c0pperdragon/Atari2600Module/EPROMer/adventure_pal.h

76,239,242,120,216,76,6,243,133,43,165,134,162,0,32,210,
240,165,136,162,1,32,210,240,165,139,162,4,32,210,240,133,
2,133,42,133,44,165,140,56,233,4,133,141,173,132,2,208,
251,169,0,133,144,133,145,133,143,133,28,169,1,133,38,169,
104,133,142,164,143,177,128,133,13,200,177,128,133,14,200,177,
128,133,15,200,132,143,133,2,169,0,133,1,76,114,240,165,
142,56,229,137,133,2,16,10,164,145,177,132,133,28,240,2,
230,145,162,0,165,142,56,229,135,16,9,164,144,177,130,170,
240,2,230,144,160,0,165,142,56,229,141,41,252,208,2,160,
2,165,142,41,15,208,38,133,2,132,31,134,27,164,143,177,
128,133,13,200,177,128,133,14,200,177,128,133,15,200,132,143,
198,142,165,142,201,8,16,167,133,1,76,198,240,133,2,132,
31,134,27,76,176,240,169,0,133,28,133,27,169,61,141,150,
2,96,160,2,56,200,233,15,176,251,73,255,233,6,10,10,
10,10,132,2,136,16,253,149,16,149,32,96,173,132,2,208,
251,169,2,133,2,133,1,133,2,133,2,133,2,133,0,133,
2,133,2,169,0,133,2,133,0,169,72,141,150,2,96,165,
138,32,113,242,160,0,177,147,133,128,160,1,177,147,133,129,
173,130,2,41,8,240,12,160,2,177,147,32,211,242,133,8,
76,60,241,160,3,177,147,32,211,242,133,8,169,8,32,211,
242,133,9,160,4,177,147,133,10,41,192,74,74,74,74,74,
133,30,74,133,29,32,53,242,165,149,201,0,240,10,201,90,
208,18,165,150,201,0,240,12,165,149,133,216,165,150,133,149,
165,216,133,150,166,149,189,68,255,133,147,189,69,255,133,148,
160,1,177,147,133,134,160,2,177,147,133,135,189,70,255,133,
147,189,71,255,133,148,160,0,177,147,133,220,189,72,255,133,
147,189,73,255,133,148,32,161,242,200,177,147,133,130,200,177,
147,133,131,173,130,2,41,8,240,11,189,74,255,32,211,242,
133,6,76,205,241,189,75,255,32,211,242,133,6,189,76,255,
9,16,133,4,166,150,189,68,255,133,147,189,69,255,133,148,
160,1,177,147,133,136,160,2,177,147,133,137,189,70,255,133,
147,189,71,255,133,148,160,0,177,147,133,220,189,72,255,133,
147,189,73,255,133,148,32,161,242,200,177,147,133,132,200,177,
147,133,133,173,130,2,41,8,240,11,189,74,255,32,211,242,
133,7,76,45,242,189,75,255,32,211,242,133,7,189,76,255,
9,16,133,5,96,164,156,169,162,133,149,133,150,152,24,105,
9,201,162,144,2,169,0,168,185,68,255,133,147,185,69,255,
133,148,162,0,161,147,197,138,208,16,165,149,201,162,208,5,
132,149,76,106,242,132,150,76,110,242,196,156,208,207,132,156,
96,133,216,133,147,169,0,133,148,24,38,147,38,148,38,147,
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
