c0pperdragon/Atari2600Module/EPROMer/atlantis_pal.h

120,216,162,255,154,232,138,149,0,232,208,251,134,211,169,1,
133,142,133,197,133,198,133,239,32,175,28,169,2,133,1,133,
2,133,0,133,2,133,2,133,2,169,0,133,0,169,75,141,
150,2,173,130,2,102,142,176,4,74,176,47,42,74,38,142,
74,36,140,144,4,38,140,208,90,16,21,165,250,41,31,133,
140,230,141,165,141,201,4,208,15,169,0,133,141,76,104,16,
165,140,69,250,41,31,240,227,76,117,16,169,1,133,142,133,
211,133,249,208,6,169,0,133,249,133,211,169,10,133,244,133,
240,169,1,133,247,32,175,28,169,0,133,239,133,238,133,236,
133,246,133,245,133,161,133,162,133,163,133,219,162,6,149,212,
202,16,251,165,211,48,4,208,44,240,26,198,242,208,22,198,
243,208,18,32,175,28,169,0,133,238,133,211,133,245,162,6,
149,212,202,16,251,162,0,134,236,134,190,134,196,165,224,208,
4,165,12,16,150,162,10,169,31,149,129,169,100,149,128,202,
202,16,244,165,239,240,15,162,10,169,110,149,128,24,105,10,
202,202,16,247,48,73,165,249,208,12,165,141,24,105,1,32,
232,30,133,128,208,57,162,0,134,158,162,2,160,8,181,161,
74,74,74,74,32,232,30,208,4,165,158,240,7,230,158,165,
143,153,130,0,181,161,41,15,32,232,30,208,4,165,158,240,
7,230,158,165,143,153,128,0,202,136,136,136,136,16,207,162,
6,134,241,181,212,240,54,201,5,240,10,165,250,41,7,208,
16,246,212,16,12,198,241,16,8,165,248,208,4,169,255,133,
211,180,212,136,224,6,208,12,185,82,30,133,155,185,87,30,
133,156,208,34,185,77,30,133,145,149,149,208,25,188,56,30,
165,250,61,70,30,208,3,188,63,30,132,145,148,149,224,6,
208,4,169,8,133,156,202,16,170,169,29,133,146,133,148,162,
2,160,152,165,211,48,10,160,128,181,221,240,4,214,221,160,
136,148,147,202,202,16,234,169,5,133,10,169,48,133,13,169,
0,133,8,133,14,133,15,169,3,133,169,166,169,181,164,56,
233,8,201,247,144,2,169,0,162,0,32,130,30,165,169,10,
170,165,143,149,170,165,144,149,171,166,169,181,164,162,1,32,
130,30,165,169,10,170,165,143,149,178,165,144,149,179,198,169,
16,201,165,190,240,4,165,164,133,190,162,4,181,186,32,194,
31,202,224,2,176,246,133,2,133,42,133,2,133,43,165,250,
41,7,208,12,165,197,41,6,208,2,169,2,73,144,133,160,
160,0,165,224,240,8,41,1,240,2,160,15,198,224,132,9,
230,250,208,8,230,251,208,4,169,243,133,252,44,133,2,16,
251,133,2,169,0,133,44,133,1,133,4,133,5,165,211,48,
7,165,219,48,6,76,2,20,76,110,19,165,250,41,7,208,
32,230,219,165,219,201,133,144,24,162,3,169,7,149,199,169,
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
