c0pperdragon/Atari2600Module/EPROMer/berzerk_pal.h

76,215,249,165,137,165,137,165,137,76,62,240,234,234,76,62,
240,165,51,5,48,5,55,41,128,36,49,80,2,9,1,149,
201,133,2,165,137,165,253,133,27,177,143,133,29,234,165,137,
165,137,196,140,144,205,196,141,176,210,177,137,133,253,200,152,
74,24,101,131,170,189,0,254,133,15,189,0,253,133,14,189,
0,251,5,225,133,13,165,230,133,28,166,254,48,24,165,137,
202,16,253,133,17,177,152,133,30,166,252,181,175,170,189,51,
255,133,230,76,139,240,177,152,133,30,166,252,181,175,170,189,
51,255,133,230,166,254,232,48,253,133,17,133,2,133,42,165,
253,133,27,177,143,133,29,234,165,137,165,137,196,140,144,99,
196,141,176,103,177,137,133,253,200,152,74,24,101,131,170,189,
0,254,133,15,189,0,253,133,14,189,0,251,5,225,133,13,
165,230,133,28,177,152,133,30,166,252,152,213,184,208,15,181,
159,133,33,181,167,133,254,169,0,133,230,76,17,240,144,26,
56,233,9,48,6,213,184,144,2,230,252,246,175,181,175,170,
189,51,255,133,230,133,2,76,143,240,192,87,176,18,169,0,
76,243,240,234,165,137,165,137,76,168,240,165,137,76,168,240,
133,2,165,253,133,27,177,143,133,29,196,141,176,4,177,137,
133,253,133,2,169,224,133,13,169,255,133,14,169,7,166,226,
224,1,208,2,169,255,133,15,133,2,165,253,133,27,169,0,
133,28,133,2,133,28,133,27,133,2,165,51,5,48,5,55,
41,128,36,49,80,2,9,1,166,252,149,201,133,2,169,0,
133,13,133,14,133,15,133,11,133,33,169,3,133,4,133,5,
169,44,69,133,133,6,133,7,169,1,133,37,133,38,162,6,
133,2,202,16,253,234,133,16,133,17,169,240,133,32,133,2,
133,42,169,6,133,232,164,232,177,234,133,27,133,2,177,236,
133,28,177,238,133,27,177,240,133,233,177,242,170,177,244,168,
165,233,133,28,134,27,132,28,133,27,198,232,16,216,169,0,
133,27,133,28,133,27,133,4,133,5,162,20,133,2,202,16,
251,169,3,133,1,169,43,141,150,2,165,129,16,3,76,185,
248,162,133,165,218,16,4,165,60,16,7,173,130,2,41,1,
208,7,164,132,169,0,76,223,249,165,128,208,2,230,128,173,
130,2,41,2,208,37,133,25,133,26,165,134,208,31,165,128,
201,18,144,2,169,0,24,248,105,1,216,133,128,133,222,169,
170,133,221,133,223,133,218,133,229,169,26,133,134,198,134,165,
218,16,23,165,132,208,2,230,133,162,3,189,245,252,69,133,
41,247,149,6,202,16,244,76,41,244,165,229,201,255,240,6,
56,102,229,76,41,244,162,0,160,3,165,157,217,141,252,240,
25,136,16,248,165,158,240,18,201,84,240,14,36,55,112,10,
36,49,112,6,48,4,36,53,16,16,165,154,201,15,240,2,
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
