c0pperdragon/Atari2600Module/EPROMer/demon_attack_pal.h

160,0,133,2,185,150,0,133,36,41,15,168,234,234,136,16,
253,181,189,133,20,165,210,37,209,133,6,133,7,169,3,133,
4,133,5,160,7,133,2,136,208,253,234,133,16,133,17,169,
240,133,32,132,33,169,1,133,37,133,38,133,2,133,42,165,
188,133,9,169,30,133,193,133,195,173,132,2,208,251,133,2,
133,1,133,43,133,44,169,9,133,220,164,220,177,221,133,27,
133,2,177,223,133,28,177,225,133,27,177,227,133,191,177,229,
170,177,231,168,165,191,133,28,134,27,132,28,132,27,198,220,
16,216,160,0,132,27,132,28,132,37,132,38,169,8,133,12,
162,204,136,132,191,230,191,133,2,172,191,0,185,141,0,133,
32,41,15,168,136,16,253,164,191,133,16,133,2,185,145,0,
133,33,41,15,168,234,234,136,16,253,164,191,133,17,133,2,
133,42,192,3,240,81,185,157,0,10,10,10,133,192,185,161,
0,10,10,10,133,194,185,197,0,133,196,169,0,196,151,208,
2,169,7,133,4,133,5,202,202,202,133,2,138,56,229,196,
168,41,248,208,14,177,192,133,27,177,194,133,28,177,205,133,
6,133,7,138,56,229,149,160,1,41,248,208,1,200,132,31,
202,228,196,144,128,176,211,165,211,37,209,133,6,165,55,133,
220,165,153,208,67,133,12,133,4,133,5,36,235,16,3,76,
178,17,165,179,10,10,10,133,192,133,2,224,12,176,5,189,
136,29,133,27,138,56,229,200,168,41,248,208,8,177,192,133,
28,177,205,133,7,138,56,229,149,160,1,41,248,208,1,200,
132,31,202,16,212,76,240,17,41,56,74,74,74,168,185,188,
29,133,192,169,29,133,193,169,0,133,4,133,5,133,2,133,
27,133,28,138,160,1,56,229,149,41,248,208,1,200,132,31,
138,74,74,176,19,74,168,176,15,192,5,176,11,185,236,29,
133,6,133,7,177,192,144,2,169,0,202,16,208,232,134,12,
240,62,169,110,133,7,165,51,133,191,133,2,224,12,176,5,
189,136,29,133,27,138,56,229,149,160,1,41,248,208,1,200,
132,31,138,201,80,176,22,74,74,74,168,138,73,255,69,189,
37,236,240,4,169,0,240,3,185,165,0,133,28,202,16,202,
162,0,133,2,134,27,134,28,134,32,169,16,133,33,165,247,
37,209,133,231,133,16,133,17,133,2,133,42,36,248,48,2,
166,237,180,242,185,174,29,133,4,185,181,29,133,5,166,212,
134,6,134,7,162,6,165,231,133,2,133,9,202,48,24,189,
156,29,192,0,240,8,133,27,192,2,144,2,133,28,198,231,
198,231,165,231,76,40,18,76,122,24,120,216,162,255,154,232,
138,149,0,232,208,251,232,134,234,32,167,26,169,171,133,129,
169,205,133,131,169,234,133,133,162,10,134,213,169,31,149,222,
202,202,16,250,76,90,20,169,2,133,1,162,25,133,2,142,
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
