c0pperdragon/Atari2600Module/EPROMer/donkey_kong_pal.h

120,216,162,255,154,232,138,149,0,232,208,251,32,138,250,169,
2,133,163,198,145,198,142,165,146,133,9,160,255,132,2,132,
1,169,64,141,150,2,230,231,169,34,160,93,162,5,149,248,
148,242,202,16,249,230,232,165,232,41,127,208,32,165,140,16,
14,165,164,248,56,233,1,133,164,216,208,3,32,163,250,165,
142,16,4,230,146,198,154,230,138,208,2,134,142,160,0,236,
128,2,208,4,165,60,48,11,132,138,165,142,16,5,132,142,
32,138,250,173,130,2,74,176,24,165,145,48,2,198,145,162,
66,169,0,149,78,202,208,251,32,138,250,169,2,133,163,208,
33,165,140,48,32,165,143,208,25,166,60,48,21,165,140,74,
176,4,165,145,16,12,169,80,133,164,162,255,134,140,132,232,
132,145,76,206,242,165,141,48,4,198,137,48,3,76,74,242,
169,2,133,137,173,128,2,166,133,240,2,165,235,133,229,166,
148,16,8,32,10,249,144,3,76,102,241,162,5,165,155,56,
233,22,144,5,202,233,28,176,251,134,237,165,229,10,48,29,
230,231,169,0,133,148,198,147,198,132,160,36,165,144,208,7,
165,237,74,176,2,160,41,196,147,144,38,176,29,176,87,230,
231,169,8,133,148,230,147,230,132,160,124,165,144,208,7,165,
237,74,144,2,160,117,196,147,176,7,132,147,132,132,76,74,
242,165,144,208,46,165,237,240,42,201,5,240,38,162,7,165,
147,164,148,208,3,24,105,1,202,48,24,221,248,253,208,248,
165,237,74,144,5,152,208,5,240,7,152,208,4,230,155,208,
2,198,155,76,239,241,165,229,41,32,208,65,198,231,165,148,
48,39,165,134,208,184,160,8,162,8,165,144,240,4,160,34,
162,16,165,155,136,202,48,166,217,205,250,208,247,165,147,56,
249,192,253,201,3,176,235,132,234,169,254,133,148,165,155,164,
234,217,0,251,208,3,76,74,242,230,155,208,66,165,229,41,
16,208,243,198,231,165,148,48,39,165,134,208,233,162,9,160,
9,165,144,240,4,160,34,162,16,165,155,136,202,48,215,217,
0,251,208,247,165,147,56,249,192,253,201,3,176,235,132,234,
169,255,133,148,165,155,164,234,217,205,250,240,93,198,155,165,
144,240,55,166,237,224,1,240,49,181,157,164,147,192,54,240,
12,192,106,208,37,201,12,176,26,105,12,16,15,201,18,176,
18,201,6,144,4,201,12,144,10,24,105,6,149,157,32,173,
250,208,7,165,133,208,3,32,163,250,165,143,208,28,165,147,
166,148,16,2,165,155,41,3,208,16,169,5,133,21,169,11,
133,25,169,2,133,143,133,139,208,76,165,133,240,72,162,4,
202,48,32,165,147,56,245,193,168,200,192,3,176,242,165,155,
56,245,128,201,4,176,233,165,236,48,11,198,236,32,173,250,
76,118,242,232,134,236,165,143,201,1,208,9,169,12,133,21,
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
