c0pperdragon/Atari2600Module/EPROMer/enduro_pal.h

120,76,107,242,24,41,15,117,200,133,189,141,34,0,165,190,
41,15,117,228,133,190,133,36,136,189,138,253,133,17,141,8,
0,76,199,240,24,41,15,117,200,133,189,141,34,0,165,190,
41,15,117,228,133,190,141,36,0,133,17,136,76,194,240,24,
41,15,117,200,133,189,141,34,0,165,190,41,15,117,228,136,
133,17,141,190,0,76,192,240,24,41,15,117,200,133,189,234,
133,34,165,190,41,15,133,17,136,76,188,240,24,41,15,117,
200,133,189,234,133,34,133,17,136,76,184,240,24,41,15,117,
200,133,189,133,17,136,76,181,240,24,41,15,136,133,17,76,
177,240,169,0,133,33,136,208,48,141,42,0,132,9,132,27,
132,29,132,28,132,31,76,63,250,141,17,0,41,15,24,234,
136,117,200,133,189,234,133,34,165,190,41,15,117,228,133,190,
133,36,189,138,253,133,8,133,6,133,42,190,120,255,177,178,
133,28,177,180,61,119,254,133,27,24,165,189,41,15,117,200,
133,189,133,34,173,190,0,41,15,117,228,133,190,133,36,196,
151,208,159,136,190,120,255,169,0,24,141,42,0,133,28,177,
180,61,119,254,133,27,136,165,189,41,15,117,200,133,189,133,
34,173,190,0,41,15,117,228,133,190,133,36,190,121,255,177,
180,136,132,185,72,164,138,177,187,133,42,133,151,185,155,0,
133,7,104,61,119,254,133,27,185,41,254,133,5,185,139,0,
133,178,165,189,41,15,117,200,133,189,133,34,165,190,41,15,
117,228,133,190,133,36,185,131,0,133,33,141,42,0,36,128,
41,15,168,185,129,253,133,226,164,185,190,120,255,177,180,61,
119,254,133,27,24,165,189,41,15,117,200,133,189,133,34,173,
190,0,41,15,117,228,133,190,133,36,198,138,136,133,42,190,
120,255,177,180,61,119,254,133,27,165,189,108,226,0,0,8,
4,12,2,10,6,14,1,9,5,13,3,11,7,15,165,198,
41,15,168,200,165,198,174,132,2,208,251,192,4,176,24,133,
2,134,31,162,48,134,13,136,208,253,133,36,133,20,234,160,
6,162,0,134,13,240,15,133,2,133,42,134,31,136,208,253,
160,6,133,36,133,20,133,2,133,42,134,254,16,31,169,0,
162,32,133,36,134,32,134,33,185,35,254,170,185,29,254,133,
2,133,42,134,27,133,28,165,254,240,2,133,9,166,192,48,
11,189,243,253,133,254,152,74,144,2,198,192,136,16,207,165,
193,133,180,169,32,133,178,164,130,165,226,162,0,133,2,133,
42,134,28,134,27,132,9,41,15,168,200,136,208,253,133,16,
165,226,133,32,133,2,133,42,160,2,132,6,169,5,133,4,
162,0,234,165,194,133,11,10,133,12,134,10,132,8,133,43,
133,44,132,29,132,31,160,102,76,28,241,169,0,170,149,0,
154,134,175,232,208,248,216,162,253,134,188,232,134,179,134,181,
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
