c0pperdragon/Atari2600Module/EPROMer/keystone_kapers_pal.h

120,216,162,255,154,232,138,149,0,232,208,251,160,12,32,44,
250,162,3,134,2,134,1,169,65,141,150,2,160,254,169,72,
149,236,169,5,149,180,148,232,202,16,243,164,142,36,135,16,
47,168,165,142,41,3,208,38,32,244,254,176,4,230,151,144,
61,169,1,133,139,133,134,42,164,151,192,16,176,8,152,41,
8,74,74,74,105,1,32,182,253,169,12,32,228,253,160,0,
165,157,201,17,144,2,160,0,132,202,160,7,36,152,48,17,
165,135,5,136,48,18,165,137,201,9,208,5,198,152,76,154,
240,152,37,142,208,2,198,138,162,255,236,128,2,240,3,232,
134,153,173,130,2,74,176,18,160,12,162,65,169,0,149,78,
202,208,251,32,44,250,198,136,48,7,32,231,252,36,136,48,
3,76,60,243,164,139,192,6,240,28,230,242,208,2,230,240,
169,127,192,5,208,2,169,3,37,142,208,10,32,244,254,48,
2,208,3,76,39,243,32,187,254,133,159,192,5,144,3,76,
56,243,36,128,16,76,80,40,168,42,42,42,56,42,42,133,
145,181,160,153,160,0,185,197,254,133,146,165,242,16,178,201,
240,176,174,173,128,2,41,32,208,167,198,145,198,145,16,27,
164,128,165,142,41,3,208,153,192,168,240,3,246,160,44,214,
160,230,145,165,145,41,31,208,136,230,146,169,15,37,128,76,
211,241,165,225,164,141,208,3,173,128,2,36,152,16,3,189,
246,252,133,158,41,32,208,5,169,7,76,126,242,165,158,10,
48,35,169,8,133,128,214,160,169,7,213,160,144,8,197,147,
208,7,169,9,149,160,76,216,241,169,154,149,160,138,74,176,
35,230,146,208,33,176,46,169,0,133,128,180,160,200,192,155,
144,6,165,147,208,6,160,153,148,160,208,76,160,8,148,160,
138,74,176,221,198,146,165,128,208,3,198,147,44,230,147,32,
77,250,76,251,241,160,6,132,149,10,10,48,40,165,147,201,
4,208,34,165,141,208,30,165,242,16,26,201,240,176,22,228,
159,208,18,181,160,233,76,201,3,176,10,230,145,230,145,169,
224,5,128,133,128,76,128,242,181,160,74,164,149,144,9,200,
192,6,144,2,160,1,132,149,165,139,208,15,192,4,208,11,
169,8,32,228,253,169,2,133,139,133,134,32,231,252,165,147,
221,9,253,208,10,165,148,197,146,208,117,198,148,16,22,221,
10,253,208,108,165,148,229,146,201,1,240,9,168,208,26,230,
148,169,80,133,144,138,74,176,8,169,120,197,144,144,10,176,
6,169,40,197,144,176,2,133,144,165,147,74,165,145,41,31,
144,2,73,255,24,125,250,251,24,73,255,117,160,201,2,176,
47,74,133,141,169,252,133,140,37,145,133,145,165,242,74,74,
41,3,5,145,133,145,41,31,224,1,240,5,73,255,24,105,
3,24,125,250,251,149,160,189,253,251,133,128,169,6,133,149,
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
