c0pperdragon/Atari2600Module/EPROMer/megamania_pal.h

120,216,162,0,169,0,149,0,154,232,208,250,32,39,255,165,
130,208,8,162,1,134,130,202,76,134,247,162,4,189,239,252,
69,134,37,135,149,136,202,16,244,232,134,10,165,136,166,218,
208,15,166,215,181,153,166,235,240,7,189,146,253,69,134,37,
135,133,212,32,139,251,165,222,74,144,54,160,5,132,167,169,
0,196,247,144,3,185,177,0,74,74,74,74,153,198,0,240,
11,170,185,241,0,24,125,42,253,32,218,251,32,129,255,133,
162,152,56,233,3,5,162,164,167,153,190,0,136,16,206,48,
121,165,240,74,74,74,74,170,165,177,61,22,253,133,198,165,
178,61,32,253,133,199,165,179,61,22,253,133,200,160,2,162,
1,134,166,185,198,0,224,1,240,4,74,74,74,74,41,7,
240,21,170,165,241,24,125,42,253,32,218,251,166,166,125,55,
253,121,57,253,32,218,251,153,204,0,166,166,240,3,153,208,
0,202,16,205,136,16,200,162,2,181,204,32,129,255,133,162,
152,56,233,3,5,162,149,190,181,208,32,129,255,133,162,152,
56,233,3,5,162,149,194,202,16,223,165,230,240,3,24,105,
46,32,129,255,133,170,136,136,136,152,5,170,133,170,165,214,
32,129,255,133,174,136,136,136,152,5,174,133,174,162,2,165,
238,32,160,255,232,165,239,32,160,255,232,165,189,32,121,255,
32,159,255,32,159,255,133,43,173,132,2,208,251,133,2,133,
42,133,1,133,5,133,2,133,42,165,136,133,9,165,138,133,
8,165,222,74,144,3,76,165,242,162,143,133,2,133,42,202,
138,56,229,249,41,248,208,2,169,2,133,31,228,161,176,235,
160,2,132,207,169,0,133,162,133,163,134,165,133,2,133,42,
185,190,0,41,15,170,208,11,169,96,133,162,234,234,133,16,
76,153,241,202,16,253,234,133,16,133,2,133,42,185,194,0,
41,15,170,208,11,169,96,133,163,234,234,133,17,76,182,241,
202,16,253,234,133,17,133,2,133,42,185,198,0,41,7,170,
134,166,189,47,253,133,5,185,198,0,74,74,74,74,170,134,
167,189,47,253,133,4,133,2,133,42,32,156,255,185,190,0,
133,32,185,194,0,133,33,166,159,165,167,208,2,166,212,134,
164,166,159,165,166,208,2,166,212,56,133,2,133,42,165,164,
133,6,134,7,165,165,233,4,170,165,162,133,32,165,163,133,
33,160,8,202,138,56,229,236,41,248,208,2,169,2,133,29,
138,56,229,237,41,248,208,2,169,2,133,30,177,175,133,2,
133,42,133,27,133,28,138,56,229,249,41,248,208,2,169,2,
133,31,141,43,0,136,16,203,164,207,36,2,112,2,132,233,
36,3,112,2,132,234,136,48,3,76,114,241,133,2,133,42,
202,169,0,133,4,133,5,165,212,133,6,133,7,133,7,32,
156,255,138,56,229,236,41,248,208,2,169,2,133,29,138,56,
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
