c0pperdragon/Atari2600Module/EPROMer/pac-man_pal.h

216,120,162,255,154,232,138,149,0,232,208,251,169,6,133,132,
10,133,236,202,134,130,134,203,32,247,251,169,203,133,204,74,
133,182,169,237,133,206,169,15,133,208,162,4,149,192,202,208,
251,133,2,169,240,133,35,169,128,133,36,162,6,202,208,253,
133,20,133,19,133,2,133,42,133,2,133,43,134,231,134,152,
76,217,247,169,0,228,217,48,9,164,220,48,5,177,223,136,
132,220,133,2,133,28,96,32,83,240,169,0,232,228,216,48,
9,164,219,48,5,177,221,136,132,219,133,2,133,27,96,133,
2,169,32,133,4,162,0,168,165,128,41,8,208,3,162,9,
234,202,16,253,133,18,132,34,132,5,162,1,169,1,24,117,
176,160,2,56,200,233,15,176,251,73,255,233,6,10,10,10,
10,133,2,136,16,253,149,16,149,32,202,16,223,133,2,133,
42,160,1,162,7,173,132,2,208,251,133,2,132,1,133,43,
165,240,133,9,132,202,136,132,135,134,201,232,169,49,133,10,
165,241,133,8,32,106,240,160,255,132,13,132,14,169,127,133,
15,76,19,243,169,0,228,217,48,9,164,220,48,5,177,223,
136,132,220,133,2,133,28,164,202,136,240,106,164,135,185,136,
0,41,15,168,185,74,253,133,212,32,106,240,169,0,133,29,
164,135,185,136,0,74,74,74,74,41,7,168,185,66,253,133,
211,32,83,240,164,135,185,136,0,16,4,169,80,208,2,169,
16,133,210,185,140,0,41,7,168,185,102,253,133,215,32,106,
240,164,135,185,140,0,74,74,74,133,213,41,7,168,185,94,
253,133,214,32,83,240,165,213,74,74,74,41,3,168,185,90,
253,133,213,76,244,241,164,135,185,144,0,41,7,168,185,126,
253,133,212,32,106,240,169,0,133,29,165,225,133,31,164,135,
185,144,0,74,74,74,41,15,168,185,110,253,133,211,32,83,
240,164,135,185,144,0,16,4,169,80,208,2,169,16,133,210,
185,148,0,41,7,168,185,102,253,133,215,32,106,240,164,135,
185,148,0,74,74,74,133,213,41,7,168,185,134,253,133,214,
32,83,240,165,225,133,30,165,213,74,74,74,168,185,74,253,
133,213,76,244,241,165,214,133,14,234,234,165,215,133,15,169,
0,76,70,242,32,106,240,165,201,201,4,208,12,169,64,5,
212,133,212,169,32,5,213,133,213,169,0,228,217,48,9,164,
220,48,5,177,223,136,132,220,133,2,133,28,165,210,133,13,
160,48,132,10,165,211,133,14,165,212,133,15,232,165,213,133,
13,228,216,48,176,165,214,133,14,164,219,48,174,165,215,133,
15,177,221,136,132,219,133,2,133,27,165,210,133,13,165,211,
133,14,165,212,133,15,234,234,165,213,133,13,228,217,48,24,
165,214,133,14,164,220,48,22,165,215,133,15,177,223,136,132,
220,133,2,133,28,76,135,242,165,214,133,14,234,234,165,215,
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
