c0pperdragon/Atari2600Module/EPROMer/pitfall_pal.h

120,216,162,0,169,0,149,0,154,232,208,250,32,117,250,162,
8,189,184,255,69,135,37,136,149,137,224,4,176,2,149,6,
202,16,238,160,80,162,144,165,227,74,144,2,162,160,169,240,
133,189,165,157,240,8,160,96,162,176,134,189,132,191,134,193,
132,195,166,148,189,149,252,16,4,165,141,133,145,160,0,189,
230,255,16,41,165,233,201,55,176,4,201,33,176,58,165,158,
208,54,165,211,74,74,72,74,74,74,74,170,104,61,146,252,
93,144,252,72,168,185,6,252,168,104,24,105,16,24,132,244,
105,6,168,162,6,165,157,73,255,133,246,185,222,251,149,160,
5,246,133,159,136,202,16,243,162,2,169,0,164,209,48,2,
181,225,32,136,243,149,149,148,152,134,219,202,16,242,166,235,
189,214,251,133,155,189,218,251,133,156,160,14,162,6,177,187,
69,135,37,136,149,167,177,183,149,174,136,202,16,240,173,132,
2,208,251,133,2,133,42,133,1,133,44,133,248,32,10,243,
162,3,160,2,32,182,243,232,160,8,32,182,243,165,128,133,
248,169,88,133,197,164,199,208,2,133,199,169,80,133,203,32,
10,243,133,2,133,42,169,0,133,38,133,27,133,28,165,142,
133,6,133,7,169,2,133,4,133,5,165,155,41,15,170,165,
156,41,15,168,133,2,133,42,234,202,16,253,133,16,165,155,
133,32,165,156,133,33,136,16,253,133,17,133,2,133,42,169,
5,133,10,160,31,165,235,10,10,170,24,165,219,101,220,133,
219,133,43,144,4,165,221,133,36,169,0,192,9,176,5,152,
74,185,197,251,133,2,133,42,133,27,133,28,176,10,189,239,
243,232,133,13,133,14,133,15,136,208,207,166,235,24,165,219,
101,220,133,219,144,2,164,221,132,36,169,1,133,10,189,206,
251,188,210,251,166,212,133,2,133,42,133,14,165,142,133,8,
169,0,133,27,133,28,133,4,133,13,132,15,134,5,162,1,
24,165,219,101,220,133,219,169,0,144,2,165,221,133,36,24,
165,219,101,220,133,219,169,0,144,2,165,221,133,2,133,42,
160,0,148,246,180,152,208,10,160,96,148,246,149,16,133,36,
208,8,136,208,253,141,36,0,149,16,133,2,133,42,202,16,
191,32,166,243,165,149,133,32,165,150,133,33,133,2,133,42,
32,166,243,165,246,133,32,165,247,133,33,165,233,24,101,242,
105,21,168,165,229,133,11,133,2,133,42,133,44,162,20,134,
37,24,165,219,101,220,133,219,169,0,133,43,144,2,165,221,
133,36,32,114,243,133,2,133,42,133,6,202,16,227,134,37,
232,134,28,240,6,169,0,133,27,240,32,162,23,24,165,219,
101,220,133,219,169,0,144,2,165,221,133,36,136,192,22,176,
228,177,181,133,27,177,185,69,135,37,136,133,2,133,42,133,
6,169,0,228,146,176,2,133,31,133,28,202,16,207,32,114,
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
