c0pperdragon/Atari2600Module/EPROMer/q-bert_pal.h

76,60,182,0,56,68,68,68,68,68,56,0,56,16,16,16,
16,48,16,0,124,64,64,56,4,68,56,0,56,68,4,24,
4,68,56,0,8,8,124,72,40,24,8,0,56,68,4,4,
120,64,124,0,56,68,68,120,64,32,28,0,32,32,32,16,
8,4,124,0,56,68,68,56,68,68,56,0,112,8,4,60,
68,68,56,165,132,133,193,165,138,133,202,10,38,132,10,38,
132,24,101,202,133,138,169,0,101,132,24,101,193,133,132,169,
0,230,138,101,132,133,132,96,0,0,0,1,1,1,1,1,
1,1,1,1,1,1,1,1,1,1,1,1,1,1,2,135,
3,207,75,135,75,135,75,135,75,135,75,135,75,135,75,135,
73,133,72,72,2,7,6,15,14,15,14,143,142,15,14,15,
14,15,14,15,14,15,12,13,8,8,0,128,128,192,192,192,
192,192,192,192,192,192,192,192,192,192,192,192,192,192,64,64,
133,44,164,167,48,44,240,42,136,190,250,186,181,0,164,169,
192,7,240,30,133,169,148,0,166,167,32,144,190,208,12,181,
171,32,222,190,149,187,148,202,76,6,177,164,197,185,198,188,
208,239,133,2,133,2,165,195,201,55,144,100,162,0,134,12,
134,27,169,16,133,33,169,3,133,4,133,38,232,134,5,164,
227,185,36,190,133,6,133,7,160,6,133,2,136,208,253,133,
16,133,17,160,7,177,147,170,133,2,133,42,177,141,133,28,
177,139,133,27,234,234,177,145,133,28,177,143,133,27,134,27,
133,43,136,16,224,32,41,187,232,134,38,134,4,134,5,134,
27,134,28,164,136,16,2,132,2,56,165,161,233,23,133,161,
169,68,133,7,165,212,133,12,165,171,32,222,190,170,132,2,
134,33,169,102,133,6,169,48,133,32,162,8,136,16,253,133,
17,134,2,202,16,253,133,16,134,2,134,42,134,2,165,195,
201,55,176,47,162,21,134,2,169,0,133,15,133,33,165,134,
133,8,164,161,177,178,133,28,198,161,138,168,189,118,191,10,
10,10,141,15,0,133,15,165,167,208,5,189,81,191,133,27,
202,16,211,232,134,33,164,161,177,178,133,2,133,28,164,188,
166,203,165,235,133,6,202,16,253,132,16,132,32,162,4,134,
2,134,42,198,161,234,161,182,161,182,189,187,191,164,161,134,
32,133,15,165,149,133,8,189,21,190,133,15,177,178,133,28,
202,16,220,162,21,132,2,138,24,101,220,168,185,0,191,133,
27,234,198,161,164,161,169,240,61,116,190,133,15,165,130,133,
8,189,9,188,133,15,177,178,133,28,202,16,216,164,161,177,
178,133,2,133,28,165,189,166,204,164,236,132,6,202,16,253,
133,16,133,32,162,4,134,2,134,42,198,161,164,161,161,182,
161,182,198,193,189,159,190,133,15,165,180,133,8,234,165,182,
133,8,134,32,177,178,133,28,202,16,219,24,162,21,134,2,
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
