c0pperdragon/Atari2600Module/EPROMer/river_raid_pal.h

120,216,162,0,169,0,149,0,154,232,208,250,32,12,255,169,
251,162,11,32,28,255,162,38,32,143,250,165,131,208,8,230,
131,133,192,169,8,133,215,162,4,165,183,74,74,74,24,105,
69,32,240,250,232,189,247,255,69,133,37,134,149,238,149,5,
202,16,242,168,165,215,201,16,240,14,173,130,2,74,144,8,
165,244,240,4,132,239,132,6,165,141,240,11,198,141,74,144,
6,169,98,37,134,133,9,232,134,242,134,4,164,179,165,224,
133,11,240,1,200,152,32,240,250,232,134,10,134,38,164,153,
165,159,133,5,133,12,32,243,250,232,165,245,32,240,250,32,
194,250,132,13,132,226,132,228,132,230,132,232,162,5,32,213,
251,165,139,201,3,176,1,202,134,222,180,160,190,200,255,134,
199,190,187,251,134,201,190,35,255,134,203,133,44,133,43,170,
56,233,1,41,31,133,252,70,252,201,26,144,4,233,22,208,
8,201,4,144,4,41,1,9,2,168,185,239,251,72,185,246,
253,72,138,74,168,177,199,144,2,177,201,224,26,176,10,224,
3,144,6,133,28,169,0,133,27,177,217,133,14,177,219,133,
15,177,203,69,133,37,134,133,7,166,222,181,142,133,237,41,
4,9,82,69,133,37,134,133,238,36,147,16,11,192,13,176,
7,185,179,255,69,133,37,134,133,8,160,160,132,253,173,132,
2,208,251,133,2,133,42,133,1,96,230,253,164,252,16,73,
166,246,240,25,165,238,76,104,241,177,186,170,169,0,240,81,
208,3,32,245,253,234,192,19,176,230,177,186,170,164,252,36,
237,16,225,185,179,255,69,133,37,134,141,242,0,177,201,133,
28,177,217,133,14,133,42,134,27,165,242,133,8,177,203,69,
133,37,134,133,7,177,219,133,15,177,199,133,28,164,253,136,
240,89,192,19,144,179,152,229,178,41,248,208,2,169,2,162,
0,136,132,253,133,2,133,42,133,29,134,27,240,61,198,252,
208,156,198,222,166,222,48,74,181,142,133,237,41,4,9,82,
69,133,37,134,133,238,181,160,170,189,200,255,133,199,169,0,
133,28,192,19,133,2,133,42,176,2,177,186,133,27,160,0,
177,217,133,14,177,219,133,15,164,253,136,240,50,189,187,251,
133,201,189,35,255,133,203,192,19,176,14,177,186,170,169,0,
240,18,232,240,201,234,56,176,26,152,229,178,41,248,208,2,
169,2,162,0,133,2,133,42,133,29,134,27,136,132,253,240,
83,166,222,32,213,251,165,238,192,19,234,133,42,133,8,176,
4,177,186,133,27,160,15,177,217,133,14,177,219,133,15,198,
253,240,49,181,154,133,242,164,253,192,19,144,52,152,229,178,
41,248,208,2,169,2,160,0,133,2,133,42,133,29,132,27,
181,148,240,19,170,224,7,176,31,202,208,253,133,17,198,253,
164,253,208,34,76,80,243,234,234,169,96,133,17,133,33,208,
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
