c0pperdragon/Atari2600Module/EPROMer/seaquest_pal.h

120,216,162,255,154,232,32,86,251,230,130,76,22,247,162,2,
164,231,185,42,252,32,203,254,162,10,189,240,252,69,133,37,
134,149,135,202,16,244,166,198,189,40,252,133,203,166,246,224,
160,144,2,162,0,189,41,252,133,247,162,3,160,8,181,158,
201,128,144,6,233,128,32,175,255,168,181,164,57,235,254,149,
168,202,16,232,160,2,152,10,10,170,185,184,0,41,240,74,
149,146,185,184,0,41,15,10,10,10,149,148,136,16,231,200,
185,146,0,208,11,169,80,153,146,0,200,200,192,10,208,240,
32,218,252,165,140,133,9,173,132,2,208,251,133,2,133,42,
133,1,166,183,181,135,133,6,133,7,133,2,133,42,32,176,
255,160,7,132,37,132,38,133,43,132,226,177,156,133,227,133,
2,133,42,177,146,133,27,177,148,133,28,177,150,133,27,177,
154,170,177,152,164,227,133,28,134,27,132,28,133,27,164,226,
136,16,214,200,162,4,133,2,133,42,132,37,132,38,132,27,
132,28,202,16,241,164,187,185,86,255,133,5,32,175,255,133,
4,162,8,189,93,255,133,2,133,42,192,0,240,2,133,27,
192,2,144,2,133,28,202,16,234,165,203,41,15,133,226,133,
2,133,42,234,234,234,165,247,41,15,170,208,9,169,96,234,
133,17,133,33,208,6,202,208,253,234,133,17,133,2,133,42,
165,247,166,203,164,226,132,226,136,16,253,141,16,0,134,32,
133,33,133,2,133,42,169,180,69,133,37,134,133,9,166,224,
189,251,252,133,152,169,253,133,153,133,147,169,253,133,149,133,
151,133,43,165,214,133,11,166,183,181,138,133,6,169,53,133,
2,133,42,133,4,164,225,166,233,240,20,189,23,255,133,6,
224,15,176,11,224,10,176,2,162,10,189,240,253,133,152,162,
9,134,12,134,7,134,44,162,9,189,230,252,69,133,37,134,
133,2,133,42,133,9,202,16,240,232,134,5,165,130,133,227,
166,224,189,251,252,105,2,133,146,162,9,136,132,226,165,227,
201,128,42,133,227,41,2,69,137,133,228,224,2,144,29,138,
168,165,228,133,2,133,42,133,9,177,146,133,28,164,226,192,
12,176,4,177,152,133,27,202,16,209,48,12,133,2,133,42,
133,9,169,0,133,28,240,237,136,165,141,136,133,2,133,42,
133,9,169,255,162,6,149,176,202,16,251,133,2,133,42,165,
137,133,9,162,3,165,7,133,248,134,229,136,192,12,133,2,
133,42,176,9,177,152,133,27,185,84,254,133,29,132,226,181,
168,240,13,168,185,81,255,24,117,158,201,160,144,2,233,96,
170,189,41,252,133,204,164,226,136,192,12,133,2,133,42,176,
9,177,152,133,27,185,84,254,133,29,169,0,170,136,192,12,
176,5,177,152,190,84,254,133,2,133,42,133,27,134,29,165,
204,41,15,170,208,9,169,96,234,133,17,133,33,208,6,202,
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
