c0pperdragon/Atari2600Module/EPROMer/space_invaders_pal.h

133,43,165,132,48,0,41,15,170,202,16,253,177,248,170,177,
238,133,27,177,240,133,28,177,242,133,27,177,244,133,28,177,
246,133,27,138,133,28,133,27,198,137,136,72,104,72,104,177,
248,170,177,238,133,27,177,240,133,28,177,242,133,27,177,244,
133,28,177,246,133,27,138,133,28,133,27,165,137,201,4,144,
4,169,0,176,3,234,169,2,141,31,0,136,16,174,200,132,
27,132,28,132,43,132,27,132,28,133,2,198,137,165,137,201,
4,144,4,169,0,176,3,234,169,2,133,31,164,128,165,2,
5,3,10,48,6,234,234,234,234,16,7,165,130,25,220,252,
133,130,133,44,136,198,140,16,9,169,0,133,37,133,38,76,
12,241,32,233,253,132,128,185,146,0,133,248,162,244,70,248,
144,7,185,214,252,101,139,208,4,72,104,169,0,149,250,232,
232,48,235,198,137,165,137,201,4,144,4,169,0,176,3,234,
169,2,133,31,165,200,41,56,74,74,74,197,128,208,22,165,
200,41,7,10,170,165,200,42,42,42,41,3,168,185,30,253,
149,238,76,250,240,162,5,202,16,253,133,43,32,178,253,162,
6,202,16,253,160,9,76,0,240,234,234,234,198,142,48,6,
32,178,253,76,12,241,36,152,112,3,76,180,241,165,221,133,
6,160,1,132,142,136,132,239,132,241,132,243,169,171,133,238,
169,180,133,240,169,189,133,242,169,17,133,2,133,43,133,244,
165,133,133,32,41,15,168,136,16,253,133,16,198,137,165,137,
201,4,169,2,144,1,74,133,31,133,2,133,42,160,0,165,
133,16,2,165,133,41,15,170,202,202,202,16,253,177,238,133,
27,234,177,240,133,27,177,242,133,27,198,244,48,18,165,244,
74,144,8,200,169,32,74,208,253,240,226,32,233,253,16,221,
169,0,133,27,133,2,165,2,10,41,128,5,130,133,130,133,
44,32,233,253,133,43,133,2,133,2,198,142,48,6,32,178,
253,76,170,241,36,152,16,3,76,132,242,32,233,253,133,43,
133,2,165,223,133,6,165,134,133,32,41,15,168,136,16,253,
133,16,133,2,165,224,133,7,165,135,133,33,41,15,168,136,
16,253,133,17,133,2,133,42,32,233,253,169,0,44,130,2,
16,2,169,5,133,5,169,0,80,2,169,5,133,4,165,152,
41,16,240,2,169,10,133,244,165,152,41,32,240,2,169,10,
133,246,165,170,74,133,2,144,23,166,201,189,22,253,133,248,
169,255,133,249,165,202,41,8,208,4,133,244,133,246,16,37,
169,0,133,248,165,202,74,74,74,165,170,41,4,240,8,169,
30,176,2,169,20,133,244,165,170,41,2,240,8,169,20,176,
2,169,30,133,246,162,9,160,9,133,2,169,0,133,13,177,
244,133,27,177,246,133,28,138,74,168,177,248,133,13,138,74,
144,13,198,137,165,137,201,4,169,2,144,1,74,133,31,202,
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
