c0pperdragon/Atari2600Module/EPROMer/venture_pal.h

169,7,133,248,164,248,190,0,255,177,237,133,27,169,0,133,
14,133,2,177,239,133,28,177,241,133,27,177,243,164,248,133,
28,134,27,134,28,134,27,165,249,133,14,198,248,16,213,166,
189,181,207,162,0,134,4,134,37,134,38,134,14,134,27,134,
28,32,128,248,166,189,181,208,162,1,32,128,248,133,2,133,
42,166,189,134,239,181,164,133,6,165,192,133,5,132,2,133,
43,200,232,181,164,133,7,181,148,133,244,16,4,181,170,133,
245,181,170,133,246,138,10,170,181,128,133,242,181,129,133,243,
166,247,165,235,133,2,208,11,196,234,208,60,165,236,133,235,
76,153,240,177,231,133,27,230,235,189,22,253,133,14,189,22,
252,133,15,36,147,112,48,234,234,234,189,167,252,133,15,189,
167,253,141,14,1,134,247,165,245,208,49,196,244,208,15,165,
246,133,245,196,154,76,244,240,234,165,189,76,153,240,234,165,
189,196,154,76,244,240,96,32,214,240,134,247,234,76,181,240,
169,0,133,31,240,22,32,214,240,76,25,241,230,245,177,242,
196,154,133,28,208,234,169,2,133,31,234,234,189,22,253,133,
14,189,22,252,133,15,152,221,87,255,208,22,112,216,189,167,
252,141,15,1,189,167,253,133,14,200,196,233,240,36,232,76,
130,240,112,10,189,167,252,133,15,189,167,253,133,14,200,192,
80,240,3,76,130,240,76,215,241,230,249,76,93,241,144,59,
208,74,232,189,22,253,133,14,165,235,208,11,196,234,208,233,
165,236,133,235,76,93,241,177,231,133,27,230,235,189,22,252,
133,15,166,189,181,209,170,41,15,133,249,138,74,74,74,74,
170,24,101,249,201,16,144,198,233,15,232,10,10,10,10,73,
112,133,33,169,0,196,154,208,183,169,2,234,133,31,202,16,
253,234,133,17,133,2,200,165,235,208,11,196,234,208,13,165,
236,133,235,76,172,241,177,231,133,27,230,235,166,189,232,165,
50,133,237,165,51,133,238,165,54,133,239,165,55,133,240,230,
247,169,0,133,245,196,154,208,2,169,2,133,2,133,42,133,
31,133,44,200,76,98,240,169,2,133,2,133,1,162,77,142,
150,2,165,219,240,7,166,217,32,0,251,198,219,173,130,2,
74,176,6,165,191,9,129,133,191,165,191,16,118,74,144,13,
173,130,2,74,144,106,162,128,32,170,248,240,99,165,204,240,
95,198,204,208,91,198,205,16,34,165,191,41,127,133,191,165,
145,201,15,240,10,36,191,112,71,169,39,133,222,208,65,169,
255,133,204,102,191,169,2,133,205,208,53,198,205,48,38,166,
216,224,9,240,2,230,216,230,206,166,206,169,6,133,250,224,
4,16,12,230,226,230,228,230,229,224,2,208,2,230,227,169,
0,133,145,240,8,198,198,16,4,230,198,240,3,32,232,248,
76,242,246,166,189,240,3,76,179,243,134,195,166,215,181,156,
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
