c0pperdragon/Atari2600Module/EPROMer/yars_revenge_pal.h

232,164,157,228,159,133,2,144,5,136,240,2,132,157,177,163,
133,28,169,0,133,15,228,154,36,154,176,2,16,20,164,155,
136,16,4,160,7,198,156,132,155,164,156,48,5,185,129,0,
133,15,232,169,0,164,169,228,170,133,2,133,15,144,5,136,
240,2,132,169,177,172,133,27,228,154,144,25,164,155,136,48,
5,234,169,0,240,4,160,7,198,156,132,155,164,156,48,5,
185,129,0,133,15,224,227,144,151,76,89,242,232,164,157,228,
159,133,2,144,5,136,240,2,132,157,177,163,133,28,138,162,
31,154,170,168,81,233,37,145,133,15,41,247,133,8,160,0,
138,229,152,48,5,201,6,176,1,152,8,132,15,232,164,169,
228,170,133,2,144,5,136,240,2,132,169,177,172,133,27,138,
73,255,168,81,233,37,145,240,5,133,15,76,194,240,169,90,
133,8,228,165,8,228,174,8,169,0,133,15,224,227,144,156,
162,255,154,76,89,242,133,2,232,169,1,133,27,133,6,228,
183,144,4,228,184,144,12,169,0,133,13,133,14,133,15,133,
9,240,16,138,168,177,233,133,13,133,14,133,15,133,8,165,
233,133,9,232,164,157,228,159,133,2,144,5,136,240,2,132,
157,177,163,133,28,224,227,208,189,76,89,242,162,6,133,2,
202,16,253,234,133,16,133,17,169,240,133,32,165,233,208,4,
169,247,133,242,133,2,133,42,169,0,133,11,133,12,133,183,
169,156,37,242,133,6,133,7,162,10,169,254,149,190,202,202,
16,250,169,224,133,236,162,48,202,133,2,208,251,134,27,134,
28,169,3,133,4,133,5,133,37,133,38,165,183,106,176,95,
169,8,36,128,112,6,240,39,16,37,133,2,165,241,240,4,
160,11,208,2,160,5,162,10,169,8,36,128,240,5,185,253,
243,208,3,185,3,244,149,189,202,136,202,16,235,48,79,162,
0,160,0,177,236,41,240,74,149,189,177,236,41,15,10,10,
10,232,232,149,189,200,232,232,192,3,208,231,160,0,162,80,
185,189,0,208,8,150,189,200,200,192,9,144,243,208,31,169,
80,133,189,133,191,133,193,133,195,133,197,160,3,177,236,41,
240,208,6,36,128,112,2,169,160,74,133,199,133,2,169,6,
133,234,164,234,177,189,133,27,133,2,177,191,133,28,177,193,
133,27,177,195,133,178,177,197,170,177,199,168,165,178,133,28,
134,27,132,28,132,27,198,234,16,216,169,0,133,27,133,28,
133,37,133,38,133,4,133,5,230,183,169,252,36,183,208,34,
162,17,169,2,197,183,208,23,162,139,74,36,128,240,21,112,
19,169,228,133,236,169,46,37,242,133,6,133,7,162,51,76,
88,241,162,51,133,2,202,208,251,133,2,169,2,133,1,162,
0,134,13,134,14,134,15,169,43,141,150,2,165,149,41,7,
201,6,208,61,36,128,112,57,165,235,41,1,170,181,60,48,
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
